steffenhauf/covscan/sketches/buzzer.png

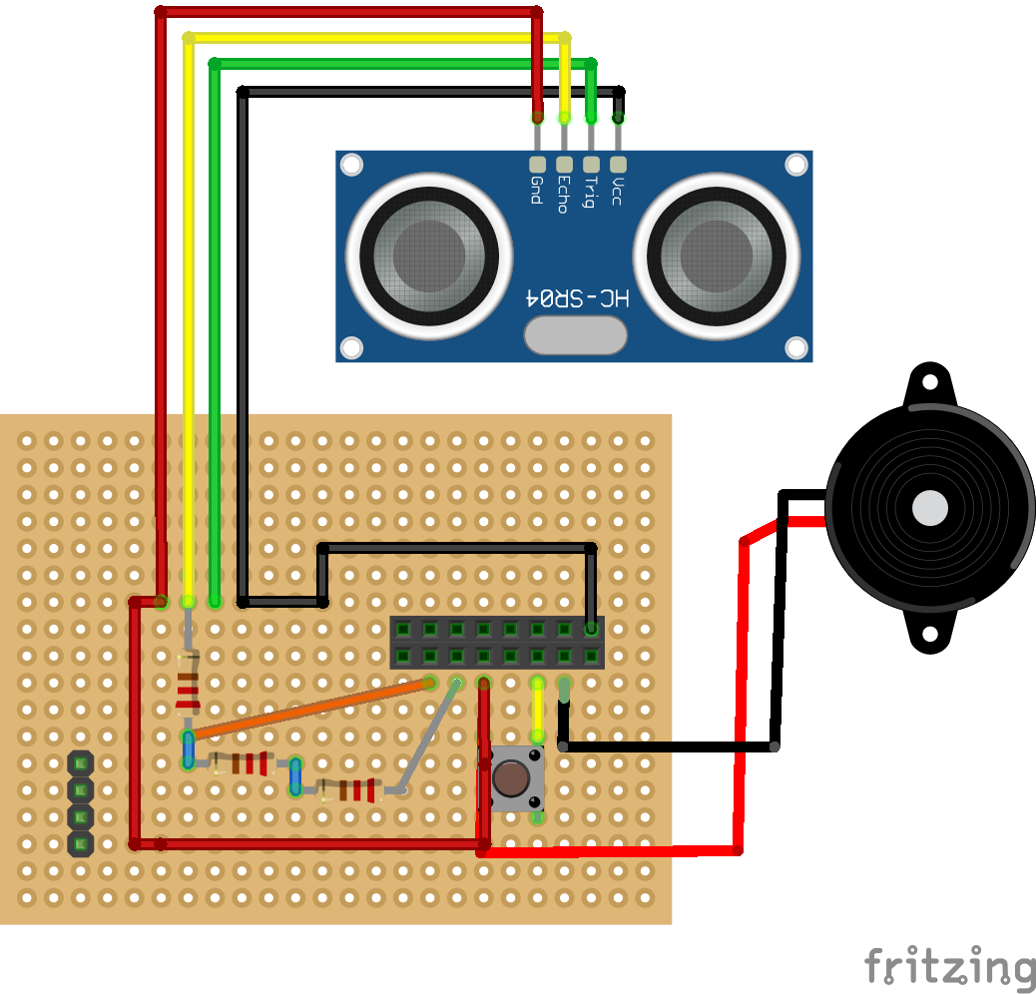
sketches/buzzer.png
